k-off/RVPC2/examples_code/OPA/OPA_Poll/User/main.c

/********************************** (C) COPYRIGHT *******************************
 * File Name          : main.c
 * Author             : WCH
 * Version            : V1.0.0
 * Date               : 2023/04/06
 * Description        : Main program body.
 *********************************************************************************
 * Copyright (c) 2021 Nanjing Qinheng Microelectronics Co., Ltd.
 * Attention: This software (modified or not) and binary are used for 
 * microcontroller manufactured by Nanjing Qinheng Microelectronics.
 *******************************************************************************/

/*
 *@Note
 *OPA positive input polling function:
 *
 *OPA2_CHN1--PA5
 *OPA2_OUT--PA4
 *P0-PA7 P1-PB3  P2-PB7
 *The number of positive terminals polling is 3, and the polling interval is 81uS.
 *When doing comparison follow-up, input different voltage values , the three positive
 *directions, and the output terminal voltage will output the positive terminal voltage according to the polling interval.
 *according to the polling interval.
 */

#include "debug.h"


/*********************************************************************
 * @fn      OPA2_Init
 *
 * @brief   Initializes OPA2.
 *
 * @return  none
 */
void OPA2_Init( void )
{
    GPIO_InitTypeDef GPIO_InitStructure = {0};
    OPA_InitTypeDef  OPA_InitStructure = {0};

    RCC_APB2PeriphClockCmd( RCC_APB2Periph_GPIOA, ENABLE );
    GPIO_InitStructure.GPIO_Pin = GPIO_Pin_5;
    GPIO_InitStructure.GPIO_Mode = GPIO_Mode_IN_FLOATING;
    GPIO_Init( GPIOA, &GPIO_InitStructure );

    OPA_InitStructure.OPA_NUM=OPA2;
    OPA_InitStructure.NSEL = CHN0;
    OPA_InitStructure.POLL_NUM=CHP_POLL_NUM_3;
    OPA_InitStructure.PSEL_POLL=CHP_OPA1_ON_OPA2_ON;
    OPA_InitStructure.OPA_POLL_Interval=0x50;
    OPA_InitStructure.Mode=OUT_IO_OUT0;
    OPA_InitStructure.FB=FB_OFF;
    OPA_Init( &OPA_InitStructure );
    OPA_Cmd(OPA2, ENABLE );
}

/*********************************************************************
 * @fn      ADC_Function_Init
 *
 * @brief   Initializes ADC collection.
 *
 * @return  none
 */
void ADC_Function_Init(void)
{
    ADC_InitTypeDef  ADC_InitStructure = {0};
    GPIO_InitTypeDef GPIO_InitStructure = {0};

    RCC_APB2PeriphClockCmd(RCC_APB2Periph_GPIOA, ENABLE);
    RCC_APB2PeriphClockCmd(RCC_APB2Periph_ADC1, ENABLE);

    GPIO_InitStructure.GPIO_Pin = GPIO_Pin_4;
    GPIO_InitStructure.GPIO_Mode = GPIO_Mode_AIN;
    GPIO_Init(GPIOA, &GPIO_InitStructure);

    ADC_DeInit(ADC1);

    ADC_CLKConfig(ADC1, ADC_CLK_Div6);

    ADC_InitStructure.ADC_Mode = ADC_Mode_Independent;
    ADC_InitStructure.ADC_ScanConvMode = DISABLE;
    ADC_InitStructure.ADC_ContinuousConvMode = DISABLE;
    ADC_InitStructure.ADC_ExternalTrigConv = ADC_ExternalTrigConv_None;
    ADC_InitStructure.ADC_DataAlign = ADC_DataAlign_Right;
    ADC_InitStructure.ADC_NbrOfChannel = 1;
    ADC_Init(ADC1, &ADC_InitStructure);

    ADC_Cmd(ADC1, ENABLE);
}

/*********************************************************************
 * @fn      Get_ADC_Val
 *
 * @brief   Returns ADCx conversion result data.
 *
 * @param   ch - ADC channel.
 *            ADC_Channel_0 - ADC Channel0 selected.
 *            ADC_Channel_1 - ADC Channel1 selected.
 *            ADC_Channel_2 - ADC Channel2 selected.
 *            ADC_Channel_3 - ADC Channel3 selected.
 *            ADC_Channel_4 - ADC Channel4 selected.
 *            ADC_Channel_5 - ADC Channel5 selected.
 *            ADC_Channel_6 - ADC Channel6 selected.
 *            ADC_Channel_7 - ADC Channel7 selected.
 *            ADC_Channel_8 - ADC Channel8 selected.
 *            ADC_Channel_9 - ADC Channel9 selected.
 *            ADC_Channel_10 - ADC Channel10 selected.
 *            ADC_Channel_11 - ADC Channel11 selected.
 *            ADC_Channel_12 - ADC Channel12 selected.
 *            ADC_Channel_13 - ADC Channel13 selected.
 *            ADC_Channel_14 - ADC Channel14 selected.
 *            ADC_Channel_15 - ADC Channel15 selected.
 *
 * @return  none
 */
u16 Get_ADC_Val(u8 ch)
{
    u16 val;

    ADC_RegularChannelConfig(ADC1, ch, 1, ADC_SampleTime_11Cycles);
    ADC_SoftwareStartConvCmd(ADC1, ENABLE);

    while(!ADC_GetFlagStatus(ADC1, ADC_FLAG_EOC));
    val = ADC_GetConversionValue(ADC1);

    return val;
}

/*********************************************************************
 * @fn      main
 *
 * @brief   Main program.
 *
 * @return  none
 */
int main(void)
{
    u16 ADC_val=0;
    SystemCoreClockUpdate();
    USART_Printf_Init(115200);
    printf("SystemClk:%d\r\n", SystemCoreClock);
    printf( "ChipID:%08x\r\n", DBGMCU_GetCHIPID() );
    OPA_POLL_Unlock();
    OPA_Unlock();
    OPA2_Init();
    ADC_Function_Init();
    while(1)
    {
        ADC_val=Get_ADC_Val(ADC_Channel_4);
        printf("ADC_val  %04d\r\n",ADC_val);
        Delay_Ms(1);
    }
}
