k-off/RVPC2/examples_code/ADC/Discontinuous_mode/User/main.c

/********************************** (C) COPYRIGHT *******************************
 * File Name          : main.c
 * Author             : WCH
 * Version            : V1.0.1
 * Date               : 2023/11/20
 * Description        : Main program body.
 *********************************************************************************
 * Copyright (c) 2021 Nanjing Qinheng Microelectronics Co., Ltd.
 * Attention: This software (modified or not) and binary are used for 
 * microcontroller manufactured by Nanjing Qinheng Microelectronics.
 *******************************************************************************/

/*
 *@Note
 *Discontinuous mode routine:
 *ADC channel 1 (PA1) - injection group channel, channel 2 (PA2) - injection group channel,
 *channel 4 (PA4) - injection group channel, this mode
 *Next, an ADC conversion is triggered by the TIM1_CC4 event, and the above-mentioned 1 injection
 *group channel is converted in sequence each time.
 *
 */

#include "debug.h"

/*********************************************************************
 * @fn      ADC_Function_Init
 *
 * @brief   Initializes ADC collection.
 *
 * @return  none
 */
void ADC_Function_Init(void)
{
    ADC_InitTypeDef  ADC_InitStructure = {0};
    GPIO_InitTypeDef GPIO_InitStructure = {0};

    RCC_APB2PeriphClockCmd(RCC_APB2Periph_GPIOA, ENABLE);
    RCC_APB2PeriphClockCmd(RCC_APB2Periph_ADC1, ENABLE);

    GPIO_InitStructure.GPIO_Pin = GPIO_Pin_1;
    GPIO_InitStructure.GPIO_Mode = GPIO_Mode_AIN;
    GPIO_Init(GPIOA, &GPIO_InitStructure);

    GPIO_InitStructure.GPIO_Pin = GPIO_Pin_2;
    GPIO_InitStructure.GPIO_Mode = GPIO_Mode_AIN;
    GPIO_Init(GPIOA, &GPIO_InitStructure);

    GPIO_InitStructure.GPIO_Pin = GPIO_Pin_4;
    GPIO_InitStructure.GPIO_Mode = GPIO_Mode_AIN;
    GPIO_Init(GPIOA, &GPIO_InitStructure);

    ADC_DeInit(ADC1);

    ADC_CLKConfig(ADC1, ADC_CLK_Div6);

    ADC_InitStructure.ADC_Mode = ADC_Mode_Independent;
    ADC_InitStructure.ADC_ScanConvMode = DISABLE;
    ADC_InitStructure.ADC_ContinuousConvMode = DISABLE;
    ADC_InitStructure.ADC_ExternalTrigConv = ADC_ExternalTrigInjecConv_T1_CC4;
    ADC_InitStructure.ADC_DataAlign = ADC_DataAlign_Right;
    ADC_InitStructure.ADC_NbrOfChannel = 1;
    ADC_Init(ADC1, &ADC_InitStructure);

    ADC_InjectedSequencerLengthConfig(ADC1, 3);
    ADC_InjectedChannelConfig(ADC1, ADC_Channel_1, 1, ADC_SampleTime_11Cycles);
    ADC_InjectedChannelConfig(ADC1, ADC_Channel_2, 2, ADC_SampleTime_11Cycles);
    ADC_InjectedChannelConfig(ADC1, ADC_Channel_4, 3, ADC_SampleTime_11Cycles);

    ADC_DiscModeChannelCountConfig(ADC1, 1);
    ADC_InjectedDiscModeCmd(ADC1, ENABLE);
    ADC_ExternalTrigInjectedConvCmd(ADC1, ENABLE);
    ADC_Cmd(ADC1, ENABLE);
}

/*********************************************************************
 * @fn      TIM1_PWM_In
 *
 * @brief   Initializes TIM1 PWM output.
 *
 * @param   arr - the period value.
 *          psc - the prescaler value.
 *          ccp - the pulse value.
 *
 * @return  none
 */
void TIM1_PWM_In(u16 arr, u16 psc, u16 ccp)
{
    GPIO_InitTypeDef        GPIO_InitStructure = {0};
    TIM_OCInitTypeDef       TIM_OCInitStructure = {0};
    TIM_TimeBaseInitTypeDef TIM_TimeBaseInitStructure = {0};

    RCC_APB2PeriphClockCmd(RCC_APB2Periph_GPIOC | RCC_APB2Periph_TIM1, ENABLE);

    GPIO_InitStructure.GPIO_Pin = GPIO_Pin_16;
    GPIO_InitStructure.GPIO_Mode = GPIO_Mode_AF_PP;
    GPIO_InitStructure.GPIO_Speed = GPIO_Speed_50MHz;
    GPIO_Init(GPIOC, &GPIO_InitStructure);

    TIM_TimeBaseInitStructure.TIM_Period = arr;
    TIM_TimeBaseInitStructure.TIM_Prescaler = psc;
    TIM_TimeBaseInitStructure.TIM_ClockDivision = TIM_CKD_DIV1;
    TIM_TimeBaseInitStructure.TIM_CounterMode = TIM_CounterMode_Up;
    TIM_TimeBaseInit(TIM1, &TIM_TimeBaseInitStructure);

    TIM_OCInitStructure.TIM_OCMode = TIM_OCMode_PWM1;
    TIM_OCInitStructure.TIM_OutputState = TIM_OutputState_Enable;
    TIM_OCInitStructure.TIM_Pulse = ccp;
    TIM_OCInitStructure.TIM_OCPolarity = TIM_OCPolarity_Low;
    TIM_OC4Init(TIM1, &TIM_OCInitStructure);

    TIM_CtrlPWMOutputs(TIM1, ENABLE);
    TIM_OC4PreloadConfig(TIM1, TIM_OCPreload_Disable);
    TIM_ARRPreloadConfig(TIM1, ENABLE);
    TIM_SelectOutputTrigger(TIM1, TIM_TRGOSource_Update);
    TIM_Cmd(TIM1, ENABLE);
}

/*********************************************************************
 * @fn      main
 *
 * @brief   Main program.
 *
 * @return  none
 */
int main(void)
{
    SystemCoreClockUpdate();
    USART_Printf_Init(115200);
    printf("SystemClk:%d\r\n", SystemCoreClock);
    printf( "ChipID:%08x\r\n", DBGMCU_GetCHIPID() );

    ADC_Function_Init();

    TIM1_PWM_In(1000, 48000 - 1, 500);

    while(1)
    {
        while(!ADC_GetFlagStatus(ADC1, ADC_FLAG_EOC));
        ADC_ClearFlag(ADC1, ADC_FLAG_EOC);
        while(!ADC_GetFlagStatus(ADC1, ADC_FLAG_JEOC));
        ADC_ClearFlag(ADC1, ADC_FLAG_JEOC);

        printf("ADC Discontinuous injected group conversion...\r\n");
        printf("%04d\r\n", (ADC1->IDATAR1));
        printf("%04d\r\n", (ADC1->IDATAR2));
        printf("%04d\r\n", (ADC1->IDATAR3));
    }
}
