k-off/RVPC2/examples_code/ADC/ExtLines_Trigger/User/main.c

/********************************** (C) COPYRIGHT *******************************
 * File Name          : main.c
 * Author             : WCH
 * Version            : V1.0.0
 * Date               : 2023/12/26
 * Description        : Main program body.
 *********************************************************************************
 * Copyright (c) 2021 Nanjing Qinheng Microelectronics Co., Ltd.
 * Attention: This software (modified or not) and binary are used for 
 * microcontroller manufactured by Nanjing Qinheng Microelectronics.
 *******************************************************************************/

/*
 *@Note
 *External lines trigger ADC conversion routine:
 *ADC channel 1 (PA1) - injection group channel, external trigger pin (PC15) high
 *level triggers EXTI line 15 event,In this mode, an ADC conversion is triggered
 *by an event on EXTI line 15, and a JEOC interrupt is generated after the conversion
 *is completed.
 *
 */

#include "debug.h"

/*********************************************************************
 * @fn      ADC_Function_Init
 *
 * @brief   Initializes ADC collection.
 *
 * @return  none
 */
void ADC_Function_Init(void)
{
    ADC_InitTypeDef  ADC_InitStructure = {0};
    GPIO_InitTypeDef GPIO_InitStructure = {0};
    NVIC_InitTypeDef NVIC_InitStructure = {0};

    RCC_APB2PeriphClockCmd(RCC_APB2Periph_GPIOA, ENABLE);
    RCC_APB2PeriphClockCmd(RCC_APB2Periph_ADC1, ENABLE);

    GPIO_InitStructure.GPIO_Pin = GPIO_Pin_1;
    GPIO_InitStructure.GPIO_Mode = GPIO_Mode_AIN;
    GPIO_Init(GPIOA, &GPIO_InitStructure);

    ADC_DeInit(ADC1);

    ADC_CLKConfig(ADC1, ADC_CLK_Div6);

    ADC_InitStructure.ADC_Mode = ADC_Mode_Independent;
    ADC_InitStructure.ADC_ScanConvMode = DISABLE;
    ADC_InitStructure.ADC_ContinuousConvMode = DISABLE;
    ADC_InitStructure.ADC_ExternalTrigConv = ADC_ExternalTrigInjecConv_Ext_IT15;
    ADC_InitStructure.ADC_DataAlign = ADC_DataAlign_Right;
    ADC_InitStructure.ADC_NbrOfChannel = 1;
    ADC_Init(ADC1, &ADC_InitStructure);

    ADC_InjectedSequencerLengthConfig(ADC1, 1);
    ADC_InjectedChannelConfig(ADC1, ADC_Channel_1, 1, ADC_SampleTime_11Cycles);
    ADC_ExternalTrigInjectedConvCmd(ADC1, ENABLE);

    NVIC_InitStructure.NVIC_IRQChannel = ADC1_IRQn;
    NVIC_InitStructure.NVIC_IRQChannelPreemptionPriority = 1;
    NVIC_InitStructure.NVIC_IRQChannelSubPriority = 0;
    NVIC_InitStructure.NVIC_IRQChannelCmd = ENABLE;
    NVIC_Init(&NVIC_InitStructure);

    ADC_ITConfig(ADC1, ADC_IT_JEOC, ENABLE);
    ADC_Cmd(ADC1, ENABLE);
}

/*********************************************************************
 * @fn      EXTI_Event_Init
 *
 * @brief   Initializes EXTI.
 *
 * @return  none
 */
void EXTI_Event_Init(void)
{
    EXTI_InitTypeDef EXTI_InitStructure = {0};
    GPIO_InitTypeDef GPIO_InitStructure = {0};

    RCC_APB2PeriphClockCmd(RCC_APB2Periph_GPIOC, ENABLE);
    RCC_APB2PeriphClockCmd(RCC_APB2Periph_AFIO, ENABLE);

    GPIO_EXTILineConfig(GPIO_PortSourceGPIOC, GPIO_PinSource15);

    GPIO_InitStructure.GPIO_Pin = GPIO_Pin_15;
    GPIO_InitStructure.GPIO_Mode = GPIO_Mode_IPD;
    GPIO_Init(GPIOC, &GPIO_InitStructure);

    EXTI_InitStructure.EXTI_Line = EXTI_Line15;
    EXTI_InitStructure.EXTI_Mode = EXTI_Mode_Event;
    EXTI_InitStructure.EXTI_Trigger = EXTI_Trigger_Rising;
    EXTI_InitStructure.EXTI_LineCmd = ENABLE;
    EXTI_Init(&EXTI_InitStructure);
}

/*********************************************************************
 * @fn      main
 *
 * @brief   Main program.
 *
 * @return  none
 */
int main(void)
{
    SystemCoreClockUpdate();
    USART_Printf_Init(115200);
    printf("SystemClk:%d\r\n", SystemCoreClock);
    printf( "ChipID:%08x\r\n", DBGMCU_GetCHIPID() );

    ADC_Function_Init();
    EXTI_Event_Init();

    while(1);
}

void ADC1_IRQHandler(void) __attribute__((interrupt("WCH-Interrupt-fast")));

/*********************************************************************
 * @fn      ADC1_IRQHandler
 *
 * @brief   ADC1 Interrupt Service Function.
 *
 * @return  none
 */
void ADC1_IRQHandler()
{
    u16 ADC_val;

    if(ADC_GetITStatus(ADC1, ADC_IT_JEOC))
    {
        printf("ADC Extline trigger conversion...\r\n");
        ADC_val = ADC_GetInjectedConversionValue(ADC1, ADC_InjectedChannel_1);
        printf("JADC%04d\r\n", ADC_val);
    }

    ADC_ClearITPendingBit(ADC1, ADC_IT_JEOC);
}
