k-off/RVPC2/examples_code/OPA/OPA_BKIN/User/main.c

/********************************** (C) COPYRIGHT *******************************
 * File Name          : main.c
 * Author             : WCH
 * Version            : V1.0.0
 * Date               : 2023/12/26
 * Description        : Main program body.
 *********************************************************************************
 * Copyright (c) 2021 Nanjing Qinheng Microelectronics Co., Ltd.
 * Attention: This software (modified or not) and binary are used for 
 * microcontroller manufactured by Nanjing Qinheng Microelectronics.
 *******************************************************************************/

/*
 *@Note
 *OPA output braking routines:
 *OPA2_CHP0--PA7
 *OPA2_CHN1--PA5
 *OPA2_OUT--PA4
 *When the output signal is high level, TIM2 brake is effective.PB9--CH1  PB6--C1N
 */

#include "debug.h"

/*********************************************************************
 * @fn      OPA2_Init
 *
 * @brief   Initializes OPA2.
 *
 * @return  none
 */
void OPA2_Init( void )
{
    GPIO_InitTypeDef GPIO_InitStructure = {0};
    OPA_InitTypeDef  OPA_InitStructure = {0};

    RCC_APB2PeriphClockCmd( RCC_APB2Periph_GPIOA, ENABLE );
    GPIO_InitStructure.GPIO_Pin = GPIO_Pin_7|GPIO_Pin_5;
    GPIO_InitStructure.GPIO_Mode = GPIO_Mode_IN_FLOATING;
    GPIO_Init( GPIOA, &GPIO_InitStructure );

    OPA_InitStructure.OPA_NUM=OPA2;
    OPA_InitStructure.PSEL = CHP0;
    OPA_InitStructure.NSEL = CHN0;
    OPA_InitStructure.Mode=OUT_IO_OUT0;
    OPA_InitStructure.PSEL_POLL=CHP_OPA1_ON_OPA2_ON;
    OPA_InitStructure.OPA_POLL_Interval=0x50;
    OPA_InitStructure.BKIN_EN=BKIN_OPA1_ON_OPA2_ON;
    OPA_InitStructure.BKIN_SEL=BKIN_OPA1_TIM2_OPA2_TIM1;
    OPA_Init( &OPA_InitStructure );
    OPA_Cmd(OPA2, ENABLE );
}

/*********************************************************************
 * @fn      TIM1_PWM_In
 *
 * @brief   Initializes TIM1 input capture.
 *
 * @param   arr - the period value.
 *          psc - the prescaler value.
 *          ccp - the pulse value.
 *
 * @return  none
 */
void TIM1_PWM_In( u16 arr, u16 psc, u16 ccp )
{
    GPIO_InitTypeDef GPIO_InitStructure;
    TIM_OCInitTypeDef TIM_OCInitStructure;
    TIM_TimeBaseInitTypeDef TIM_TimeBaseInitStructure;
    TIM_BDTRInitTypeDef TIM_BDTRInitStructure;
    RCC_APB1PeriphClockCmd(RCC_APB1Periph_TIM2, ENABLE);

    RCC_APB2PeriphClockCmd( RCC_APB2Periph_GPIOA  | RCC_APB2Periph_GPIOB | RCC_APB2Periph_TIM1 , ENABLE );

    GPIO_InitStructure.GPIO_Pin = GPIO_Pin_9|GPIO_Pin_6;
    GPIO_InitStructure.GPIO_Mode = GPIO_Mode_AF_PP;
    GPIO_InitStructure.GPIO_Speed = GPIO_Speed_50MHz;
    GPIO_Init( GPIOB, &GPIO_InitStructure );

    TIM_TimeBaseInitStructure.TIM_Period = arr;
    TIM_TimeBaseInitStructure.TIM_Prescaler = psc;
    TIM_TimeBaseInitStructure.TIM_ClockDivision = TIM_CKD_DIV1;
    TIM_TimeBaseInitStructure.TIM_CounterMode = TIM_CounterMode_Up;
    TIM_TimeBaseInit( TIM1, &TIM_TimeBaseInitStructure);
    TIM_OCInitStructure.TIM_OCMode = TIM_OCMode_PWM2;
    TIM_OCInitStructure.TIM_OutputState = TIM_OutputState_Enable;
    TIM_OCInitStructure.TIM_OutputNState = TIM_OutputNState_Enable;
    TIM_OCInitStructure.TIM_Pulse = ccp;
    TIM_OCInitStructure.TIM_OCPolarity = TIM_OCPolarity_High;
    TIM_OCInitStructure.TIM_OCNPolarity = TIM_OCNPolarity_Low;
    TIM_OCInitStructure.TIM_OCIdleState = TIM_OCIdleState_Set;
    TIM_OCInitStructure.TIM_OCNIdleState = TIM_OCNIdleState_Set;
    TIM_OC1Init( TIM1, &TIM_OCInitStructure );

    TIM_BDTRInitStructure.TIM_OSSIState = TIM_OSSIState_Enable;
    TIM_BDTRInitStructure.TIM_OSSRState = TIM_OSSRState_Enable;
    TIM_BDTRInitStructure.TIM_LOCKLevel = TIM_LOCKLevel_OFF;
    TIM_BDTRInitStructure.TIM_DeadTime = 0x01;
    TIM_BDTRInitStructure.TIM_Break = TIM_Break_Enable;
    TIM_BDTRInitStructure.TIM_BreakPolarity = TIM_BreakPolarity_High;
    TIM_BDTRInitStructure.TIM_AutomaticOutput = TIM_AutomaticOutput_Disable;
    TIM_BDTRConfig( TIM1, &TIM_BDTRInitStructure );

    TIM_CtrlPWMOutputs(TIM1, ENABLE );
    TIM_OC1PreloadConfig( TIM1, TIM_OCPreload_Disable );
    TIM_ARRPreloadConfig( TIM1, ENABLE );
    TIM_Cmd( TIM1, ENABLE );
}

/*********************************************************************
 * @fn      main
 *
 * @brief   Main program.
 *
 * @return  none
 */
int main(void)
{
    NVIC_PriorityGroupConfig(NVIC_PriorityGroup_1);
    SystemCoreClockUpdate();
    Delay_Init();
    USART_Printf_Init(115200);
    printf("SystemClk:%d\r\n", SystemCoreClock);
    printf( "ChipID:%08x\r\n", DBGMCU_GetCHIPID() );
    OPA_POLL_Unlock();
    OPA_Unlock();
    OPA2_Init();
    TIM1_PWM_In( 1000, 4800-1, 500 );

    while(1);
}
