k-off/RVPC2/examples_code/PWR/Standby_Mode/User/main.c

/********************************** (C) COPYRIGHT *******************************
 * File Name          : main.c
 * Author             : WCH
 * Version            : V1.0.0
 * Date               : 2023/12/26
 * Description        : Main program body.
 *********************************************************************************
 * Copyright (c) 2021 Nanjing Qinheng Microelectronics Co., Ltd.
 * Attention: This software (modified or not) and binary are used for 
 * microcontroller manufactured by Nanjing Qinheng Microelectronics.
 *******************************************************************************/

/*
 *@Note
 *low power, standby mode routine:
 *AWU automatically wakes up
 *This example demonstrates that WFI enters standby mode and wakes up automatically.
 *Note: In order to reduce power consumption as much as possible, it is recommended
 *to set the unused GPIO to pull-up mode.
 *
 */

#include "debug.h"

/* Global define */

/* Global Variable */

/*********************************************************************
 * @fn      EXTI_INT_INIT
 *
 * @brief   Initializes EXTI collection.
 *
 * @return  none
 */
void EXTI_INT_INIT(void)
{
    EXTI_InitTypeDef EXTI_InitStructure = {0};

    RCC_APB2PeriphClockCmd(RCC_APB2Periph_AFIO, ENABLE);

    EXTI_InitStructure.EXTI_Line = EXTI_Line27;
    EXTI_InitStructure.EXTI_Mode = EXTI_Mode_Interrupt;
    EXTI_InitStructure.EXTI_Trigger = EXTI_Trigger_Falling;
    EXTI_InitStructure.EXTI_LineCmd = ENABLE;
    EXTI_Init(&EXTI_InitStructure);
}

/*********************************************************************
 * @fn      main
 *
 * @brief   Main program.
 *
 * @return  none
 */
int main(void)
{
    GPIO_InitTypeDef GPIO_InitStructure = {0};
    NVIC_InitTypeDef NVIC_InitStructure = {0};

    NVIC_PriorityGroupConfig(NVIC_PriorityGroup_1);
    SystemCoreClockUpdate();
    Delay_Init();
    Delay_Ms(1000);

    USART_Printf_Init(115200);
    printf("SystemClk:%d\r\n", SystemCoreClock);
    printf( "ChipID:%08x\r\n", DBGMCU_GetCHIPID() );
    printf("Standby Mode Test\r\n");

    Delay_Ms(1000);
    EXTI_INT_INIT();

    RCC_APB2PeriphClockCmd(RCC_APB2Periph_GPIOA | RCC_APB2Periph_GPIOB | RCC_APB2Periph_GPIOC | RCC_APB2Periph_AFIO, ENABLE);
    RCC_APB1PeriphClockCmd(RCC_APB1Periph_PWR, ENABLE);
    GPIO_PinRemapConfig(GPIO_Remap_SWJ_Disable, ENABLE);
    GPIO_InitStructure.GPIO_Pin = GPIO_Pin_All;
    GPIO_InitStructure.GPIO_Mode = GPIO_Mode_IPU;

    GPIO_Init(GPIOA, &GPIO_InitStructure);
    GPIO_Init(GPIOB, &GPIO_InitStructure);
    GPIO_Init(GPIOC, &GPIO_InitStructure);

    NVIC_InitStructure.NVIC_IRQChannel = AWU_IRQn;
    NVIC_InitStructure.NVIC_IRQChannelPreemptionPriority = 1;
    NVIC_InitStructure.NVIC_IRQChannelSubPriority = 0;
    NVIC_InitStructure.NVIC_IRQChannelCmd = ENABLE;
    NVIC_Init(&NVIC_InitStructure);

    AWU_SetPrescaler(AWU_Prescaler_10240);
    AWU_SetWindowValue(25);  // 25/(48M/1024/10240) = 5.46s
    AutoWakeUpCmd(ENABLE);

    PWR_EnterSTANDBYMode();

    while(1)
    {
        Delay_Ms(1000);
        printf("Run in main\r\n");
    }
}

void AWU_IRQHandler(void) __attribute__((interrupt("WCH-Interrupt-fast")));

/*********************************************************************
 * @fn      AWU_IRQHandler
 *
 * @brief   AWU Interrupt Service Function.
 *
 * @return  none
 */
void AWU_IRQHandler()
{
    EXTI_ClearITPendingBit(EXTI_Line27);
    SystemInit();
    RCC_APB2PeriphClockCmd(RCC_APB2Periph_AFIO, ENABLE);
    GPIO_PinRemapConfig(GPIO_Remap_SWJ_Disable, DISABLE);
    USART_Printf_Init(115200);
    printf("\r\n Auto wake up \r\n");
}
