k-off/RVPC2/examples_code/IAP/USB_UART/CH32X035_IAP/User/main.c

/********************************** (C) COPYRIGHT *******************************
 * File Name          : main.c
 * Author             : WCH
 * Version            : V1.0.0
 * Date               : 2024/03/07
 * Description        : Main program body.
 *********************************************************************************
 * Copyright (c) 2021 Nanjing Qinheng Microelectronics Co., Ltd.
 * Attention: This software (modified or not) and binary are used for 
 * microcontroller manufactured by Nanjing Qinheng Microelectronics.
 *******************************************************************************/
/*
 *@Note
 *IAP upgrade routine:
 *Support serial port and USB for FLASH burning
 *
 *1. Use the IAP download tool to realize the download PA0 floating (default pull-up input)
 *2. After downloading the APP, connect PA0 to ground (low level input), and press
 *the reset button to run the APP program.
 *3. The routine needs to install the CH372 driver.
 *
*/

#include "ch32x035_usbfs_device.h"
#include "debug.h"
#include "iap.h"


/*********************************************************************
 * @fn      IAP_2_APP
 *
 * @brief   IAP_2_APP program.
 *
 * @return  none
 */
void IAP_2_APP(void) {
    USBFS_Device_Init(DISABLE,PWR_VDD_SupplyVoltage());
    GPIO_Cfg_Float();
    RCC_APB2PeriphClockCmd( RCC_APB2Periph_AFIO, DISABLE );
    RCC_AHBPeriphClockCmd( RCC_AHBPeriph_USBFS, DISABLE );
    RCC_APB1PeriphClockCmd(RCC_APB1Periph_USART2,DISABLE);

    Delay_Ms(50);
    printf("jump APP\r\n");
    Delay_Ms(10);
    NVIC_EnableIRQ(Software_IRQn);
    NVIC_SetPendingIRQ(Software_IRQn);
}

/*********************************************************************
 * @fn      main
 *
 * @brief   Main program.
 *
 * @return  none
 */
int main(void)
{
    SystemCoreClockUpdate();
    Delay_Init();
    USART_Printf_Init(115200);
    printf("SystemClk:%d\r\n", SystemCoreClock);
    printf("ChipID:%08x\r\n", DBGMCU_GetCHIPID() );

    if(PA0_Check() == 0){
        Delay_Ms(10);
        IAP_2_APP();
        while(1);
    }

    /* Usb Init */
    USBFS_RCC_Init( );
    USBFS_Device_Init( ENABLE ,PWR_VDD_SupplyVoltage());

    USART2_CFG(57600);
    while(1)
    {
        if( USART_GetFlagStatus(USART2, USART_FLAG_RXNE) != RESET) {
            UART_Rx_Deal();
        }
        if (End_Flag)
        {
            Delay_Ms(10);
            IAP_2_APP();
            while(1);
        }
    }
}
