k-off/RVPC2/examples_code/USB/USBFS/DEVICE/CompositeKM/User/ch32x035_usbfs_device.c

/********************************** (C) COPYRIGHT *******************************
* File Name          : ch32x035_usbfs_device.c
* Author             : WCH
* Version            : V1.0.0
* Date               : 2024/04/16
* Description        : This file provides all the USBFS firmware functions.
*********************************************************************************
* Copyright (c) 2021 Nanjing Qinheng Microelectronics Co., Ltd.
* Attention: This software (modified or not) and binary are used for 
* microcontroller manufactured by Nanjing Qinheng Microelectronics.
*******************************************************************************/

#include <ch32x035_usbfs_device.h>
#include "usbd_composite_km.h"

/*******************************************************************************/
/* Variable Definition */

/* Global */
const    uint8_t  *pUSBFS_Descr;

/* Setup Request */
volatile uint8_t  USBFS_SetupReqCode;
volatile uint8_t  USBFS_SetupReqType;
volatile uint16_t USBFS_SetupReqValue;
volatile uint16_t USBFS_SetupReqIndex;
volatile uint16_t USBFS_SetupReqLen;

/* USB Device Status */
volatile uint8_t  USBFS_DevConfig;
volatile uint8_t  USBFS_DevAddr;
volatile uint8_t  USBFS_DevSleepStatus;
volatile uint8_t  USBFS_DevEnumStatus;

/* HID Class Command */
volatile uint8_t  USBFS_HidIdle[ 2 ];
volatile uint8_t  USBFS_HidProtocol[ 2 ];

/* Endpoint Buffer */
__attribute__ ((aligned(4))) uint8_t USBFS_EP0_Buf[ DEF_USBD_UEP0_SIZE ];     //ep0(64)
__attribute__ ((aligned(4))) uint8_t USBFS_EP1_Buf[ DEF_USB_EP1_FS_SIZE ];    //ep1_in(64)
__attribute__ ((aligned(4))) uint8_t USBFS_EP2_Buf[ DEF_USB_EP2_FS_SIZE ];    //ep2_in(64)

/* USB IN Endpoint Busy Flag */
volatile uint8_t  USBFS_Endp_Busy[ DEF_UEP_NUM ];



/******************************************************************************/
/* Interrupt Service Routine Declaration*/
void USBFS_IRQHandler(void) __attribute__((interrupt("WCH-Interrupt-fast")));


/*********************************************************************
 * @fn      USBFS_RCC_Init
 *
 * @brief   Initializes the USBFS clock configuration.
 *
 * @return  none
 */
void USBFS_RCC_Init(void)
{
    RCC_APB2PeriphClockCmd( RCC_APB2Periph_AFIO, ENABLE );
    RCC_AHBPeriphClockCmd( RCC_AHBPeriph_USBFS, ENABLE );
}

/*********************************************************************
 * @fn      USBFS_Device_Endp_Init
 *
 * @brief   Initializes USB device endpoints.
 *
 * @return  none
 */
void USBFS_Device_Endp_Init( void )
{
    USBFSD->UEP4_1_MOD = USBFS_UEP1_TX_EN;
    USBFSD->UEP2_3_MOD = USBFS_UEP2_TX_EN;

    USBFSD->UEP0_DMA = (uint32_t)USBFS_EP0_Buf;
    USBFSD->UEP1_DMA = (uint32_t)USBFS_EP1_Buf;
    USBFSD->UEP2_DMA = (uint32_t)USBFS_EP2_Buf;

    USBFSD->UEP0_CTRL_H = USBFS_UEP_R_RES_ACK | USBFS_UEP_T_RES_NAK;
    USBFSD->UEP1_CTRL_H = USBFS_UEP_T_RES_NAK;
    USBFSD->UEP2_CTRL_H = USBFS_UEP_T_RES_NAK;

    /* Clear End-points Busy Status */
    for(uint8_t i=0; i<DEF_UEP_NUM; i++ )
    {
        USBFS_Endp_Busy[ i ] = 0;
    }
}

/*********************************************************************
 * @fn      GPIO_USB_INIT
 *
 * @brief   Initializes USB GPIO.
 *
 * @return  none
 */
void GPIO_USB_INIT(void)
{
    GPIO_InitTypeDef GPIO_InitStructure = {0};

    RCC_APB2PeriphClockCmd(RCC_APB2Periph_GPIOC, ENABLE);
    GPIO_InitStructure.GPIO_Pin = GPIO_Pin_16;
    GPIO_InitStructure.GPIO_Mode = GPIO_Mode_IN_FLOATING;
    GPIO_Init(GPIOC, &GPIO_InitStructure);

    GPIO_InitStructure.GPIO_Pin = GPIO_Pin_17;
    GPIO_InitStructure.GPIO_Mode = GPIO_Mode_IPU;
    GPIO_Init(GPIOC, &GPIO_InitStructure);
}

/*********************************************************************
 * @fn      USBFS_Device_Init
 *
 * @brief   Initializes USB device.
 *
 * @return  none
 */
void USBFS_Device_Init( FunctionalState sta , PWR_VDD VDD_Voltage)
{
    if( sta )
    {
        GPIO_USB_INIT();
        if( VDD_Voltage == PWR_VDD_5V )
        {
            AFIO->CTLR = (AFIO->CTLR & ~(UDP_PUE_MASK | UDM_PUE_MASK | USB_PHY_V33)) | UDP_PUE_10K | USB_IOEN;
        }
        else
        {
            AFIO->CTLR = (AFIO->CTLR & ~(UDP_PUE_MASK | UDM_PUE_MASK )) | USB_PHY_V33 | UDP_PUE_1K5 | USB_IOEN;
        }

        USBFSD->BASE_CTRL = 0x00;
        USBFS_Device_Endp_Init( );
        USBFSD->DEV_ADDR = 0x00;
        USBFSD->BASE_CTRL = USBFS_UC_DEV_PU_EN | USBFS_UC_INT_BUSY | USBFS_UC_DMA_EN;
        USBFSD->INT_FG = 0xff;
        USBFSD->UDEV_CTRL = USBFS_UD_PD_DIS | USBFS_UD_PORT_EN;
        USBFSD->INT_EN = USBFS_UIE_SUSPEND | USBFS_UIE_BUS_RST | USBFS_UIE_TRANSFER;
        NVIC_EnableIRQ( USBFS_IRQn );
    }
    else
    {
        AFIO->CTLR = AFIO->CTLR & ~(UDP_PUE_MASK | UDM_PUE_MASK | USB_IOEN);
        USBFSD->BASE_CTRL = USBFS_UC_RESET_SIE | USBFS_UC_CLR_ALL;
        Delay_Us( 10 );
        USBFSD->BASE_CTRL = 0x00;
        NVIC_DisableIRQ( USBFS_IRQn );
    }
}

/*********************************************************************
 * @fn      USBFS_Endp_DataUp
 *
 * @brief   USBFS device data upload
 *
 * @return  none
 */
uint8_t USBFS_Endp_DataUp(uint8_t endp, uint8_t *pbuf, uint16_t len, uint8_t mod)
{
    uint8_t endp_mode;
    uint8_t buf_load_offset;
    uint16_t* uep_tx_len;
    uint16_t* uep_ctrl;
    uint8_t* uep_dma;

    switch ( endp )
    {
        case 1:
            uep_tx_len = (uint16_t*)&USBFSD->UEP1_TX_LEN;
            uep_ctrl = (uint16_t*)&USBFSD->UEP1_CTRL_H;
            uep_dma = (uint8_t*)&USBFSD->UEP1_DMA;
            break;
        case 2:
            uep_tx_len = (uint16_t*)&USBFSD->UEP2_TX_LEN;
            uep_ctrl = (uint16_t*)&USBFSD->UEP2_CTRL_H;
            uep_dma = (uint8_t*)&USBFSD->UEP2_DMA;
            break;
        case 3:
            uep_tx_len = (uint16_t*)&USBFSD->UEP3_TX_LEN;
            uep_ctrl = (uint16_t*)&USBFSD->UEP3_CTRL_H;
            uep_dma = (uint8_t*)&USBFSD->UEP3_DMA;
            break;
        case 4:
            uep_tx_len = (uint16_t*)&USBFSD->UEP4_TX_LEN;
            uep_ctrl = (uint16_t*)&USBFSD->UEP4_CTRL_H;
            uep_dma = (uint8_t*)&USBFSD->UEP0_DMA;
            break;
        case 5:
            uep_tx_len = (uint16_t*)&USBFSD->UEP5_TX_LEN;
            uep_ctrl = (uint16_t*)&USBFSD->UEP5_CTRL_H;
            uep_dma = (uint8_t*)&USBFSD->UEP5_DMA;
            break;
        case 6:
            uep_tx_len = (uint16_t*)&USBFSD->UEP6_TX_LEN;
            uep_ctrl = (uint16_t*)&USBFSD->UEP6_CTRL_H;
            uep_dma = (uint8_t*)&USBFSD->UEP6_DMA;
            break;
        case 7:
            uep_tx_len = (uint16_t*)&USBFSD->UEP7_TX_LEN;
            uep_ctrl = (uint16_t*)&USBFSD->UEP7_CTRL_H;
            uep_dma = (uint8_t*)&USBFSD->UEP7_DMA;
            break;
        default:
            break;
    }

    /* DMA config, endp_ctrl config, endp_len config */
    if( ( endp >= DEF_UEP1 ) && ( endp <= DEF_UEP7 ) )
    {
        if( USBFS_Endp_Busy[ endp ] == 0 )
        {
            if( (endp == DEF_UEP1) || (endp == DEF_UEP4) )
            {
                /* endp1/endp4 */
                endp_mode = USBFSD->UEP4_1_MOD;
                if( endp == DEF_UEP1 )
                {
                    endp_mode = (uint8_t)( endp_mode >> 4 );
                }
            }
            else if( ( endp == DEF_UEP2 ) || ( endp == DEF_UEP3 ) )
            {
                /* endp2/endp3 */
                endp_mode = USBFSD->UEP2_3_MOD;
                if( endp == DEF_UEP3 )
                {
                    endp_mode = (uint8_t)( endp_mode >> 4 );
                }
            }
            else
            {
                /* endp5/endp6/endp7 */
                endp_mode = USBFSD->UEP567_MOD;
                if( endp == DEF_UEP5 )
                {
                    endp_mode = (uint8_t)( endp_mode << 2 );
                }
                else if ( endp == DEF_UEP7 )
                {
                    endp_mode = (uint8_t)( endp_mode >> 2 );
                }

                endp_mode &= 0xfe;
            }

            if( endp_mode & USBFSD_UEP_TX_EN )
            {
                if( endp_mode & USBFSD_UEP_RX_EN )
                {
                    if( endp_mode & USBFSD_UEP_BUF_MOD )
                    {
                        if( *uep_ctrl & USBFS_UEP_T_TOG )
                        {
                            buf_load_offset = 192;
                        }
                        else
                        {
                            buf_load_offset = 128;
                        }
                    }
                    else
                    {
                        buf_load_offset = 64;
                    }
                }
                else
                {
                    if( endp_mode & USBFSD_UEP_BUF_MOD )
                    {
                        /* double tx buffer */
                        if( *uep_ctrl & USBFS_UEP_T_TOG )
                        {
                            buf_load_offset = 64;
                        }
                        else
                        {
                            buf_load_offset = 0;
                        }
                    }
                    else
                    {
                        buf_load_offset = 0;
                    }
                }

                if( endp == DEF_UEP4 )
                {
                    buf_load_offset += 64;
                }

                if( buf_load_offset == 0 )
                {
                    if( mod == DEF_UEP_DMA_LOAD )
                    {
                        /* DMA mode */
                        *uep_dma = (uint16_t)(uint32_t)pbuf;
                    }
                    else
                    {
                        /* copy mode */
                        memcpy( ((uint8_t *)(*((volatile uint32_t *)( uep_dma ))) + 0x20000000), pbuf, len );
                    }
                }
                else
                {
                    memcpy( ((uint8_t *)(*((volatile uint32_t *)( uep_dma ))) + 0x20000000) + buf_load_offset, pbuf, len );
                }
                /* tx length */
                *uep_tx_len = len;
                /* response ack */
                *uep_ctrl = ( *uep_ctrl & ~USBFS_UEP_T_RES_MASK ) | USBFS_UEP_T_RES_ACK;

                /* Set end-point busy */
                USBFS_Endp_Busy[ endp ] = 0x01;

            }
            else
            {
                return 1;
            }
        }
        else
        {
            return 1;
        }
    }
    else
    {
        return 1;
    }
    return 0;
}

/*********************************************************************
 * @fn      USBFS_IRQHandler
 *
 * @brief   This function handles HD-FS exception.
 *
 * @return  none
 */
void USBFS_IRQHandler( void )
{

    uint8_t  intflag, intst, errflag;
    uint16_t len;

    intflag = USBFSD->INT_FG;
    intst = USBFSD->INT_ST;

    if( intflag & USBFS_UIF_TRANSFER )
    {
        switch( intst & USBFS_UIS_TOKEN_MASK )
        {
            /* data-in stage processing */
            case USBFS_UIS_TOKEN_IN:
                switch( intst & ( USBFS_UIS_TOKEN_MASK | USBFS_UIS_ENDP_MASK ) )
                {
                    /* end-point 0 data in interrupt */
                    case USBFS_UIS_TOKEN_IN | DEF_UEP0:
                        if( USBFS_SetupReqLen == 0 )
                        {
                            USBFSD->UEP0_CTRL_H = USBFS_UEP_R_TOG | USBFS_UEP_R_RES_ACK;
                        }

                        if ( ( USBFS_SetupReqType & USB_REQ_TYP_MASK ) != USB_REQ_TYP_STANDARD )
                        {
                            /* Non-standard request endpoint 0 Data upload */
                        }
                        else
                        {
                            switch( USBFS_SetupReqCode )
                            {
                                case USB_GET_DESCRIPTOR:
                                    len = USBFS_SetupReqLen >= DEF_USBD_UEP0_SIZE ? DEF_USBD_UEP0_SIZE : USBFS_SetupReqLen;
                                    memcpy( USBFS_EP0_Buf, pUSBFS_Descr, len );
                                    USBFS_SetupReqLen -= len;
                                    pUSBFS_Descr += len;
                                    USBFSD->UEP0_TX_LEN = len;
                                    USBFSD->UEP0_CTRL_H ^= USBFS_UEP_T_TOG;
                                    break;

                                case USB_SET_ADDRESS:
                                    USBFSD->DEV_ADDR = ( USBFSD->DEV_ADDR & USBFS_UDA_GP_BIT ) | USBFS_DevAddr;
                                    break;

                                default:
                                    break;
                            }
                        }
                        break;

                    /* end-point 1 data in interrupt */
                    case USBFS_UIS_TOKEN_IN | DEF_UEP1:
                        USBFSD->UEP1_CTRL_H = ( USBFSD->UEP1_CTRL_H & ~USBFS_UEP_T_RES_MASK ) | USBFS_UEP_T_RES_NAK;
                        USBFSD->UEP1_CTRL_H ^= USBFS_UEP_T_TOG;
                        USBFS_Endp_Busy[ DEF_UEP1 ] = 0;
                        break;

                    /* end-point 2 data in interrupt */
                    case USBFS_UIS_TOKEN_IN | DEF_UEP2:
                        USBFSD->UEP2_CTRL_H = ( USBFSD->UEP2_CTRL_H & ~USBFS_UEP_T_RES_MASK ) | USBFS_UEP_T_RES_NAK;
                        USBFSD->UEP2_CTRL_H ^= USBFS_UEP_T_TOG;
                        USBFS_Endp_Busy[ DEF_UEP2 ] = 0;
                        break;

                    default :
                        break;
                }
                break;

            /* data-out stage processing */
            case USBFS_UIS_TOKEN_OUT:
                switch( intst & ( USBFS_UIS_TOKEN_MASK | USBFS_UIS_ENDP_MASK ) )
                {
                    /* end-point 0 data out interrupt */
                    case USBFS_UIS_TOKEN_OUT | DEF_UEP0:
                        if( intst & USBFS_UIS_TOG_OK )
                        {
                            if( ( USBFS_SetupReqType & USB_REQ_TYP_MASK ) != USB_REQ_TYP_STANDARD )
                            {
                                if( ( USBFS_SetupReqType & USB_REQ_TYP_MASK ) == USB_REQ_TYP_CLASS )
                                {
                                    switch( USBFS_SetupReqCode )
                                    {
                                        case HID_SET_REPORT:
                                            KB_LED_Cur_Status = USBFS_EP0_Buf[ 0 ];
                                            USBFS_SetupReqLen = 0;
                                            break;
                                        default:
                                            break;
                                    }
                                }
                            }
                            else
                            {
                                /* Standard request end-point 0 Data download */
                                /* Add your code here */
                            }
                        }
                        if( USBFS_SetupReqLen == 0 )
                        {
                            USBFSD->UEP0_TX_LEN  = 0;
                            USBFSD->UEP0_CTRL_H = USBFS_UEP_T_TOG | USBFS_UEP_T_RES_ACK;
                        }
                        break;

                    default:
                        break;
                }
                break;

            /* Setup stage processing */
            case USBFS_UIS_TOKEN_SETUP:
                USBFSD->UEP0_CTRL_H = USBFS_UEP_T_TOG|USBFS_UEP_T_RES_NAK|USBFS_UEP_R_TOG|USBFS_UEP_R_RES_NAK;


                /* Store All Setup Values */
                USBFS_SetupReqType  = pUSBFS_SetupReqPak->bRequestType;
                USBFS_SetupReqCode  = pUSBFS_SetupReqPak->bRequest;
                USBFS_SetupReqLen   = pUSBFS_SetupReqPak->wLength;
                USBFS_SetupReqValue = pUSBFS_SetupReqPak->wValue;
                USBFS_SetupReqIndex = pUSBFS_SetupReqPak->wIndex;
                len = 0;
                errflag = 0;

                if( ( USBFS_SetupReqType & USB_REQ_TYP_MASK ) != USB_REQ_TYP_STANDARD )
                {
                    if( ( USBFS_SetupReqType & USB_REQ_TYP_MASK ) == USB_REQ_TYP_CLASS )
                    {
                        /* Class Request */
                        switch( USBFS_SetupReqCode )
                        {
                            case HID_SET_REPORT:
                                break;

                            case HID_SET_IDLE:
                                if( USBFS_SetupReqIndex == 0x00 )
                                {
                                    USBFS_HidIdle[ 0 ] = (uint8_t)( USBFS_SetupReqValue >> 8 );
                                }
                                else if( USBFS_SetupReqIndex == 0x01 )
                                {
                                    USBFS_HidIdle[ 1 ] = (uint8_t)( USBFS_SetupReqValue >> 8 );
                                }
                                else
                                {
                                    errflag = 0xFF;
                                }
                                break;

                            case HID_SET_PROTOCOL:
                                if( USBFS_SetupReqIndex == 0x00 )
                                {
                                    USBFS_HidProtocol[ 0 ] = (uint8_t)USBFS_SetupReqValue;
                                }
                                else if( USBFS_SetupReqIndex == 0x01 )
                                {
                                    USBFS_HidProtocol[ 1 ] = (uint8_t)USBFS_SetupReqValue;
                                }
                                else
                                {
                                    errflag = 0xFF;
                                }
                                break;

                            case HID_GET_IDLE:
                                if( USBFS_SetupReqIndex == 0x00 )
                                {
                                    USBFS_EP0_Buf[ 0 ] = USBFS_HidIdle[ 0 ];
                                    len = 1;
                                }
                                else if( USBFS_SetupReqIndex == 0x01 )
                                {
                                    USBFS_EP0_Buf[ 0 ] = USBFS_HidIdle[ 1 ];
                                    len = 1;
                                }
                                else
                                {
                                    errflag = 0xFF;
                                }
                                break;

                            case HID_GET_PROTOCOL:
                                if( USBFS_SetupReqIndex == 0x00 )
                                {
                                    USBFS_EP0_Buf[ 0 ] = USBFS_HidProtocol[ 0 ];
                                    len = 1;
                                }
                                else if( USBFS_SetupReqIndex == 0x01 )
                                {
                                    USBFS_EP0_Buf[ 0 ] = USBFS_HidProtocol[ 1 ];
                                    len = 1;
                                }
                                else
                                {
                                    errflag = 0xFF;
                                }
                                break;

                            default:
                                errflag = 0xFF;
                                break;
                        }
                    }
                }
                else
                {
                    /* usb standard request processing */
                    switch( USBFS_SetupReqCode )
                    {
                        /* get device/configuration/string/report/... descriptors */
                        case USB_GET_DESCRIPTOR:
                            switch( (uint8_t)( USBFS_SetupReqValue >> 8 ) )
                            {
                                /* get usb device descriptor */
                                case USB_DESCR_TYP_DEVICE:
                                    pUSBFS_Descr = MyDevDescr;
                                    len = DEF_USBD_DEVICE_DESC_LEN;
                                    break;

                                /* get usb configuration descriptor */
                                case USB_DESCR_TYP_CONFIG:
                                    pUSBFS_Descr = MyCfgDescr;
                                    len = DEF_USBD_CONFIG_DESC_LEN;
                                    break;

                                /* get usb hid descriptor */
                                case USB_DESCR_TYP_HID:
                                    if( USBFS_SetupReqIndex == 0x00 )
                                    {
                                        pUSBFS_Descr = &MyCfgDescr[ 18 ];
                                        len = 9;
                                    }
                                    else if( USBFS_SetupReqIndex == 0x01 )
                                    {
                                        pUSBFS_Descr = &MyCfgDescr[ 43 ];
                                        len = 9;
                                    }
                                    else
                                    {
                                        errflag = 0xFF;
                                    }
                                    break;

                                /* get usb report descriptor */
                                case USB_DESCR_TYP_REPORT:
                                    if( USBFS_SetupReqIndex == 0x00 )
                                    {
                                        pUSBFS_Descr = KeyRepDesc;
                                        len = DEF_USBD_REPORT_DESC_LEN_KB;
                                    }
                                    else if( USBFS_SetupReqIndex == 0x01 )
                                    {
                                        pUSBFS_Descr = MouseRepDesc;
                                        len = DEF_USBD_REPORT_DESC_LEN_MS;
                                    }
                                    else
                                    {
                                        errflag = 0xFF;
                                    }
                                    break;

                                /* get usb string descriptor */
                                case USB_DESCR_TYP_STRING:
                                    switch( (uint8_t)( USBFS_SetupReqValue & 0xFF ) )
                                    {
                                        /* Descriptor 0, Language descriptor */
                                        case DEF_STRING_DESC_LANG:
                                            pUSBFS_Descr = MyLangDescr;
                                            len = DEF_USBD_LANG_DESC_LEN;
                                            break;

                                        /* Descriptor 1, Manufacturers String descriptor */
                                        case DEF_STRING_DESC_MANU:
                                            pUSBFS_Descr = MyManuInfo;
                                            len = DEF_USBD_MANU_DESC_LEN;
                                            break;

                                        /* Descriptor 2, Product String descriptor */
                                        case DEF_STRING_DESC_PROD:
                                            pUSBFS_Descr = MyProdInfo;
                                            len = DEF_USBD_PROD_DESC_LEN;
                                            break;

                                        /* Descriptor 3, Serial-number String descriptor */
                                        case DEF_STRING_DESC_SERN:
                                            pUSBFS_Descr = MySerNumInfo;
                                            len = DEF_USBD_SN_DESC_LEN;
                                            break;

                                        default:
                                            errflag = 0xFF;
                                            break;
                                    }
                                    break;

                                default :
                                    errflag = 0xFF;
                                    break;
                            }

                            /* Copy Descriptors to Endp0 DMA buffer */
                            if( USBFS_SetupReqLen > len )
                            {
                                USBFS_SetupReqLen = len;
                            }
                            len = ( USBFS_SetupReqLen >= DEF_USBD_UEP0_SIZE ) ? DEF_USBD_UEP0_SIZE : USBFS_SetupReqLen;
                            memcpy( USBFS_EP0_Buf, pUSBFS_Descr, len );
                            pUSBFS_Descr += len;
                            break;

                        /* Set usb address */
                        case USB_SET_ADDRESS:
                            USBFS_DevAddr = (uint8_t)( USBFS_SetupReqValue & 0xFF );
                            break;

                        /* Get usb configuration now set */
                        case USB_GET_CONFIGURATION:
                            USBFS_EP0_Buf[ 0 ] = USBFS_DevConfig;
                            if( USBFS_SetupReqLen > 1 )
                            {
                                USBFS_SetupReqLen = 1;
                            }
                            break;

                        /* Set usb configuration to use */
                        case USB_SET_CONFIGURATION:
                            USBFS_DevConfig = (uint8_t)( USBFS_SetupReqValue & 0xFF );
                            USBFS_DevEnumStatus = 0x01;
                            break;

                        /* Clear or disable one usb feature */
                        case USB_CLEAR_FEATURE:
                            if( ( USBFS_SetupReqType & USB_REQ_RECIP_MASK ) == USB_REQ_RECIP_DEVICE )
                            {
                                /* clear one device feature */
                                if( (uint8_t)( USBFS_SetupReqValue & 0xFF ) == USB_REQ_FEAT_REMOTE_WAKEUP )
                                {
                                    /* clear usb sleep status, device not prepare to sleep */
                                    USBFS_DevSleepStatus &= ~0x01;
                                }
                                else
                                {
                                    errflag = 0xFF;
                                }
                            }
                            else if( ( USBFS_SetupReqType & USB_REQ_RECIP_MASK ) == USB_REQ_RECIP_ENDP )
                            {
                                if( (uint8_t)( USBFS_SetupReqValue & 0xFF ) == USB_REQ_FEAT_ENDP_HALT )
                                {
                                    /* Clear End-point Feature */
                                    switch( (uint8_t)( USBFS_SetupReqIndex & 0xFF ) )
                                    {
                                        case ( DEF_UEP_IN | DEF_UEP1 ):
                                            /* Set End-point 1 OUT ACK */
                                            USBFSD->UEP1_CTRL_H = USBFS_UEP_T_RES_NAK;
                                            break;

                                        case ( DEF_UEP_IN | DEF_UEP2 ):
                                            /* Set End-point 2 IN NAK */
                                            USBFSD->UEP2_CTRL_H = USBFS_UEP_T_RES_NAK;
                                            break;

                                        default:
                                            errflag = 0xFF;
                                            break;
                                    }
                                }
                                else
                                {
                                    errflag = 0xFF;
                                }
                            }
                            else
                            {
                                errflag = 0xFF;
                            }
                            break;

                        /* set or enable one usb feature */
                        case USB_SET_FEATURE:
                            if( ( USBFS_SetupReqType & USB_REQ_RECIP_MASK ) == USB_REQ_RECIP_DEVICE )
                            {
                                /* Set Device Feature */
                                if( (uint8_t)( USBFS_SetupReqValue & 0xFF ) == USB_REQ_FEAT_REMOTE_WAKEUP )
                                {
                                    if( MyCfgDescr[ 7 ] & 0x20 )
                                    {
                                        /* Set Wake-up flag, device prepare to sleep */
                                        USBFS_DevSleepStatus |= 0x01;
                                    }
                                    else
                                    {
                                        errflag = 0xFF;
                                    }
                                }
                                else
                                {
                                    errflag = 0xFF;
                                }
                            }
                            else if( ( USBFS_SetupReqType & USB_REQ_RECIP_MASK ) == USB_REQ_RECIP_ENDP )
                            {
                                /* Set Endpoint Feature */
                                if( (uint8_t)( USBFS_SetupReqValue & 0xFF ) == USB_REQ_FEAT_ENDP_HALT )
                                {
                                    switch( (uint8_t)( USBFS_SetupReqIndex & 0xFF ) )
                                    {
                                        case ( DEF_UEP_IN | DEF_UEP1 ):
                                            USBFSD->UEP1_CTRL_H = ( USBFSD->UEP1_CTRL_H & ~USBFS_UEP_T_RES_MASK ) | USBFS_UEP_T_RES_STALL;
                                            break;

                                        case ( DEF_UEP_IN | DEF_UEP2 ):
                                            USBFSD->UEP2_CTRL_H = ( USBFSD->UEP2_CTRL_H & ~USBFS_UEP_T_RES_MASK ) | USBFS_UEP_T_RES_STALL;
                                            break;

                                        default:
                                            errflag = 0xFF;
                                            break;
                                    }
                                }
                                else
                                {
                                    errflag = 0xFF;
                                }
                            }
                            else
                            {
                                errflag = 0xFF;
                            }
                            break;

                        /* This request allows the host to select another setting for the specified interface  */
                        case USB_GET_INTERFACE:
                            USBFS_EP0_Buf[ 0 ] = 0x00;
                            if( USBFS_SetupReqLen > 1 )
                            {
                                USBFS_SetupReqLen = 1;
                            }
                            break;

                        case USB_SET_INTERFACE:
                            break;

                        /* host get status of specified device/interface/end-points */
                        case USB_GET_STATUS:
                            USBFS_EP0_Buf[ 0 ] = 0x00;
                            USBFS_EP0_Buf[ 1 ] = 0x00;
                            if( ( USBFS_SetupReqType & USB_REQ_RECIP_MASK ) == USB_REQ_RECIP_DEVICE )
                            {
                                if( USBFS_DevSleepStatus & 0x01 )
                                {
                                    USBFS_EP0_Buf[ 0 ] = 0x02;
                                }
                                else
                                {
                                    USBFS_EP0_Buf[ 0 ] = 0x00;
                                }
                            }
                            else if( ( USBFS_SetupReqType & USB_REQ_RECIP_MASK ) == USB_REQ_RECIP_ENDP )
                            {
                                if( (uint8_t)( USBFS_SetupReqIndex & 0xFF ) == ( DEF_UEP_IN | DEF_UEP1 ) )
                                {
                                    if( ( USBFSD->UEP1_CTRL_H & USBFS_UEP_T_RES_MASK ) == USBFS_UEP_T_RES_STALL )
                                    {
                                        USBFS_EP0_Buf[ 0 ] = 0x01;
                                    }
                                }
                                else if( (uint8_t)( USBFS_SetupReqIndex & 0xFF ) == ( DEF_UEP_IN | DEF_UEP2 ) )
                                {
                                    if( ( USBFSD->UEP2_CTRL_H & USBFS_UEP_T_RES_MASK ) == USBFS_UEP_T_RES_STALL )
                                    {
                                        USBFS_EP0_Buf[ 0 ] = 0x01;
                                    }
                                }
                                else
                                {
                                    errflag = 0xFF;
                                }
                            }
                            else
                            {
                                errflag = 0xFF;
                            }
                            if( USBFS_SetupReqLen > 2 )
                            {
                                USBFS_SetupReqLen = 2;
                            }
                            break;

                        default:
                            errflag = 0xFF;
                            break;
                    }
                }

                /* errflag = 0xFF means a request not support or some errors occurred, else correct */
                if( errflag == 0xFF )
                {
                    /* if one request not support, return stall */
                    USBFSD->UEP0_CTRL_H = USBFS_UEP_T_TOG | USBFS_UEP_T_RES_STALL|USBFS_UEP_R_TOG | USBFS_UEP_R_RES_STALL;
                }
                else
                {
                    /* end-point 0 data Tx/Rx */
                    if( USBFS_SetupReqType & DEF_UEP_IN )
                    {
                        len = ( USBFS_SetupReqLen > DEF_USBD_UEP0_SIZE )? DEF_USBD_UEP0_SIZE : USBFS_SetupReqLen;
                        USBFS_SetupReqLen -= len;
                        USBFSD->UEP0_TX_LEN = len;
                        USBFSD->UEP0_CTRL_H = USBFS_UEP_T_TOG | USBFS_UEP_T_RES_ACK;
                    }
                    else
                    {
                        if( USBFS_SetupReqLen == 0 )
                        {
                            USBFSD->UEP0_TX_LEN = 0;
                            USBFSD->UEP0_CTRL_H = USBFS_UEP_T_TOG | USBFS_UEP_T_RES_ACK;
                        }
                        else
                        {
                            USBFSD->UEP0_CTRL_H = USBFS_UEP_R_TOG | USBFS_UEP_R_RES_ACK;
                        }
                    }
                }
                break;

            /* Sof pack processing */
            case USBFS_UIS_TOKEN_SOF:
                break;

            default :
                break;
        }
        USBFSD->INT_FG = USBFS_UIF_TRANSFER;
    }
    else if( intflag & USBFS_UIF_BUS_RST )
    {
        /* usb reset interrupt processing */
        USBFS_DevConfig = 0;
        USBFS_DevAddr = 0;
        USBFS_DevSleepStatus = 0;
        USBFS_DevEnumStatus = 0;

        USBFSD->DEV_ADDR = 0;
        USBFS_Device_Endp_Init( );
        USBFSD->INT_FG = USBFS_UIF_BUS_RST;
    }
    else if( intflag & USBFS_UIF_SUSPEND )
    {
        USBFSD->INT_FG = USBFS_UIF_SUSPEND;
        Delay_Us(10);
        /* usb suspend interrupt processing */
        if( USBFSD->MIS_ST & USBFS_UMS_SUSPEND )
        {
            USBFS_DevSleepStatus |= 0x02;
            if( USBFS_DevSleepStatus == 0x03 )
            {
                /* Handling usb sleep here */
                MCU_Sleep_Wakeup_Operate( );
            }
        }
        else
        {
            USBFS_DevSleepStatus &= ~0x02;
        }
    }
    else
    {
        /* other interrupts */
        USBFSD->INT_FG = intflag;
    }
}

/*********************************************************************
 * @fn      USBFS_Send_Resume
 *
 * @brief   USBFS device sends wake-up signal to host
 *
 * @return  none
 */
void USBFS_Send_Resume(void)
{
    if(PWR_VDD_SupplyVoltage() == PWR_VDD_5V)
    {
        GPIOC->BSXR = 0x00020001;
        GPIOC->CFGXR = (GPIOC->CFGXR & ~0x000000FF) | 0x00000088;
        AFIO->CTLR = (AFIO->CTLR & ~UDP_PUE_10K ) | UDM_PUE_10K;
        Delay_Ms( 8 );
        AFIO->CTLR = (AFIO->CTLR & ~UDM_PUE_10K ) | UDP_PUE_10K;
        GPIOC->CFGXR = (GPIOC->CFGXR & ~0x000000FF) | 0x00000084;
        GPIOC->BSXR = 0x00010002;
    }
    else
    {
        GPIOC->BSXR = 0x00020001;
        GPIOC->CFGXR = (GPIOC->CFGXR & ~0x000000FF) | 0x00000088;
        AFIO->CTLR = (AFIO->CTLR & ~UDP_PUE_1K5 ) | UDM_PUE_1K5;
        Delay_Ms( 8 );
        AFIO->CTLR = (AFIO->CTLR & ~UDM_PUE_1K5 ) | UDP_PUE_1K5;
        GPIOC->CFGXR = (GPIOC->CFGXR & ~0x000000FF) | 0x00000084;
        GPIOC->BSXR = 0x00010002;
    }
}
