k-off/RVPC2/examples_code/IAP/USB_UART/CH32X035_IAP/User/ch32x035_it.c

/********************************** (C) COPYRIGHT *******************************
 * File Name          : ch32x035_it.c
 * Author             : WCH
 * Version            : V1.0.0
 * Date               : 2024/10/28
 * Description        : Main Interrupt Service Routines.
*********************************************************************************
* Copyright (c) 2021 Nanjing Qinheng Microelectronics Co., Ltd.
* Attention: This software (modified or not) and binary are used for 
* microcontroller manufactured by Nanjing Qinheng Microelectronics.
*******************************************************************************/
#include "ch32x035_it.h"

void NMI_Handler(void) __attribute__((interrupt("WCH-Interrupt-fast")));
void HardFault_Handler(void) __attribute__((interrupt("WCH-Interrupt-fast")));

/*********************************************************************
 * @fn      NMI_Handler
 *
 * @brief   This function handles NMI exception.
 *
 * @return  none
 */
void NMI_Handler(void)
{
    while (1)
  {
  }
}

/*********************************************************************
 * @fn      HardFault_Handler
 *
 * @brief   This function handles Hard Fault exception.
 *
 * @return  none
 */
void HardFault_Handler(void)
{
  printf("HardFault_Handler\r\n");
  NVIC_SystemReset();
  while (1)
  {
  }
}
